flummer/benchpsu-v2/Images/bench_top_psu_v2-8711.jpg

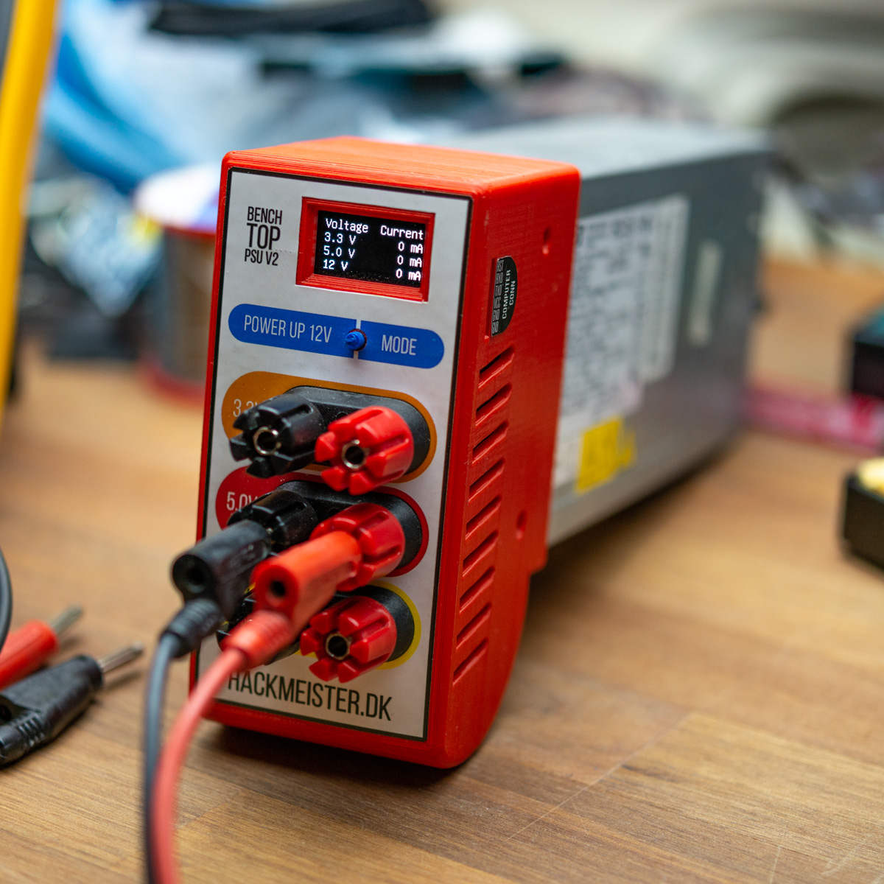
Images/bench_top_psu_v2-8711.jpg
